hogehogei/ESP32_MusicPlayer/main/Util/Log.hpp

#ifndef    LOG_HPP_INCLUDED
#define    LOG_HPP_INCLUDED

struct LogTagName 
{
    static inline constexpr char sk_BT_AV[] = "BT_AV";
    static inline constexpr char sk_BT_A2DP[] = "BT_A2DP";
    static inline constexpr char sk_BT_AVRCP[] = "BT_AVRCP";
    static inline constexpr char sk_BT_APPCORE[] = "BT_APPCORE";
};

#endif      // LOG_HPP_INCLUDED
